ddenhart/ece411-practicum-2014/Project Model/ECE411_T10_LED_output_sequence_diagram.png

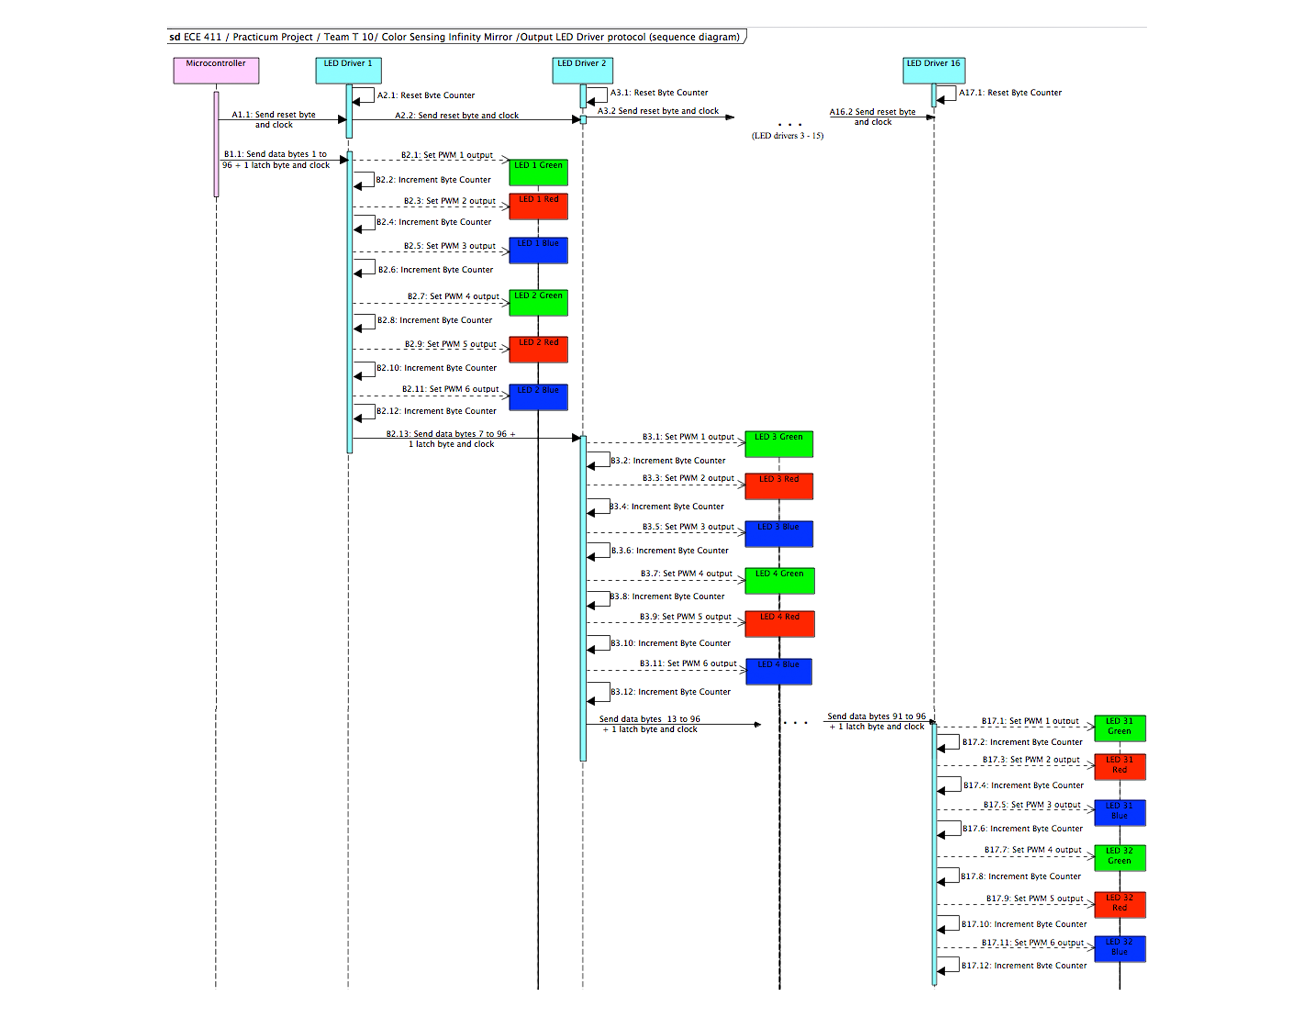
Project Model/ECE411_T10_LED_output_sequence_diagram.png
