ddenhart/ece411-practicum-2014/Project Model/T10-L0-AudioAmplifier.png

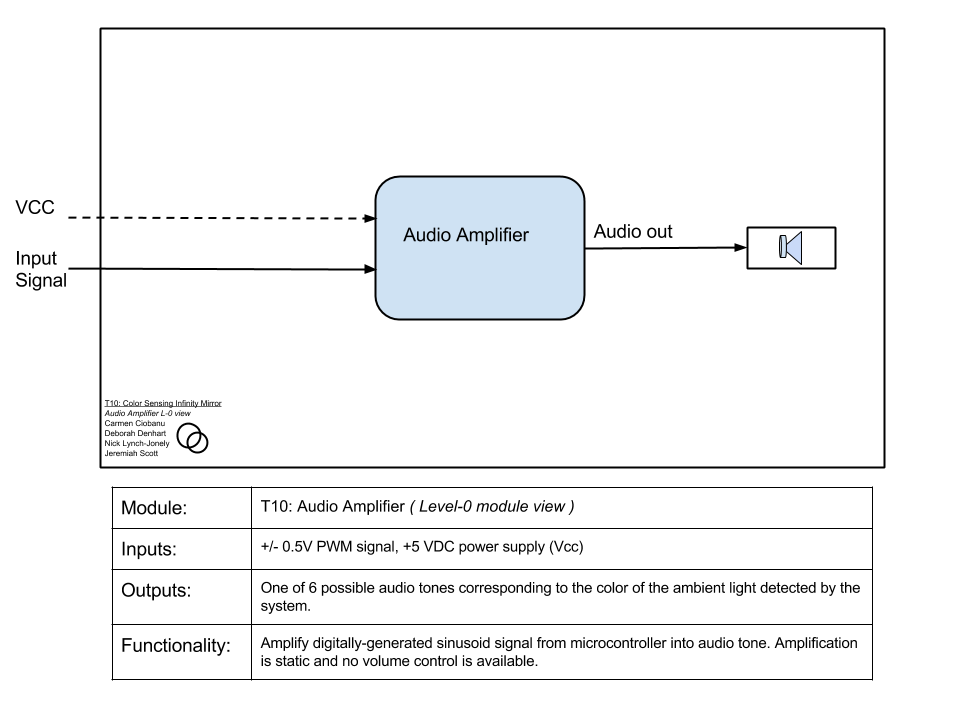
Project Model/T10-L0-AudioAmplifier.png
