ddenhart/ece411-practicum-2014/Project Model/T10-L0-blockdiagram_colorsensor.png

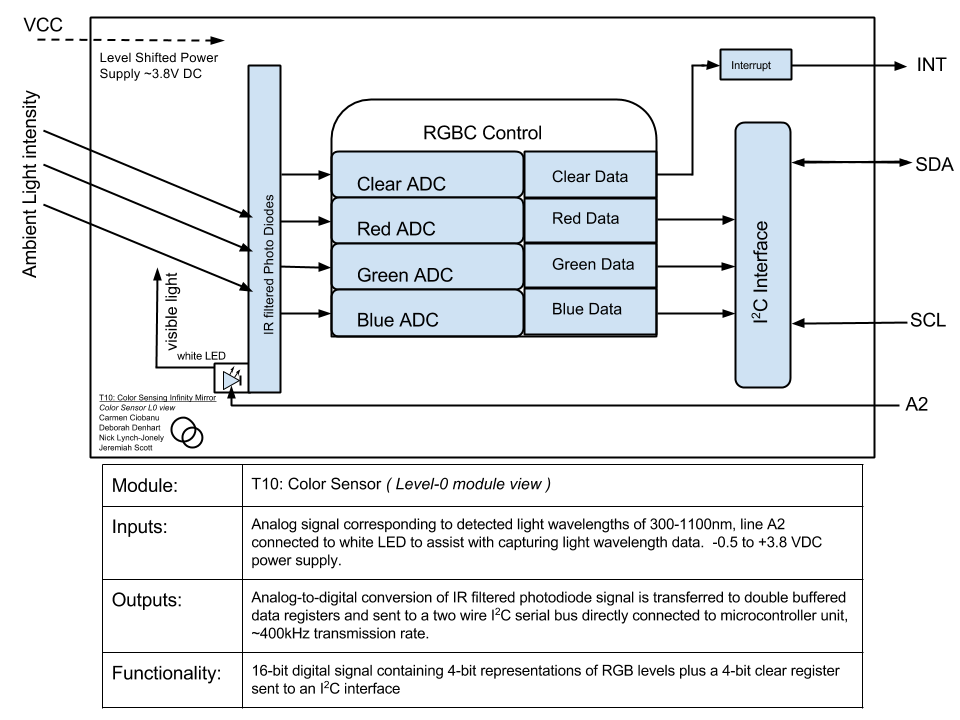
Project Model/T10-L0-blockdiagram_colorsensor.png
