ddenhart/ece411-practicum-2014/Project Model/T10-L0-blockdiagram_RGBLEDstrip.png

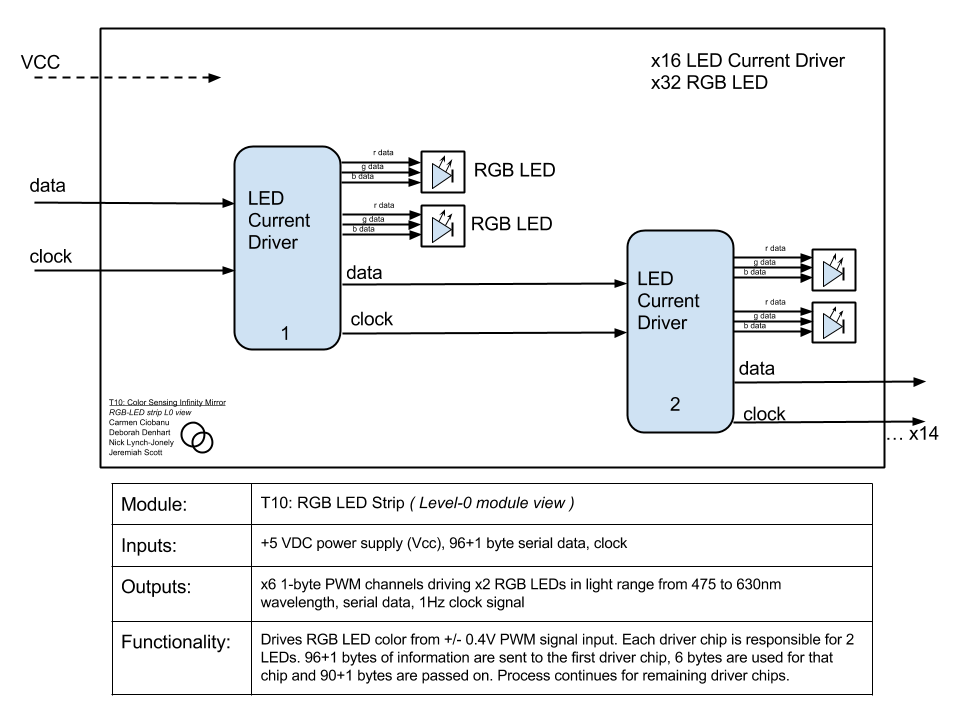
Project Model/T10-L0-blockdiagram_RGBLEDstrip.png
