ddenhart/ece411-practicum-2014/Project Model/T10-L1-blockdiagram_fullsystem.png

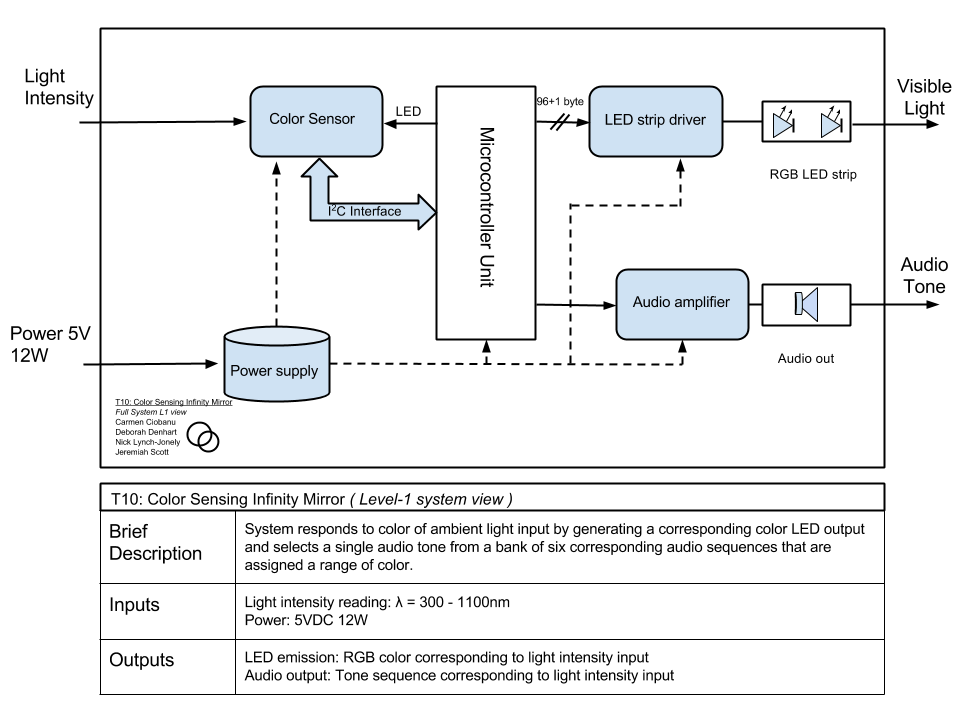
Project Model/T10-L1-blockdiagram_fullsystem.png
