ddenhart/ece411-practicum-2014/Project Model/T10_UML_activity_view_colorsensor.png

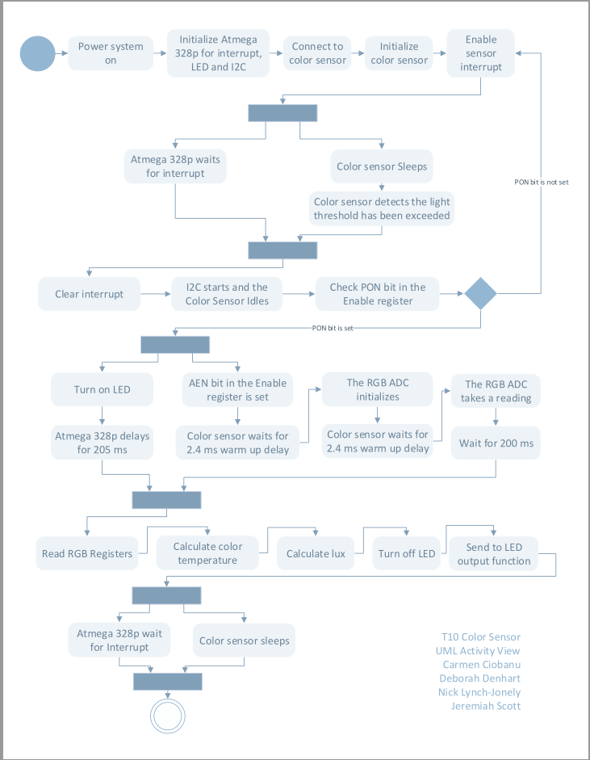
Project Model/T10_UML_activity_view_colorsensor.png
