ddenhart/ece411-practicum-2014/prototyping stage/colorSensorBlockDiagram.JPG

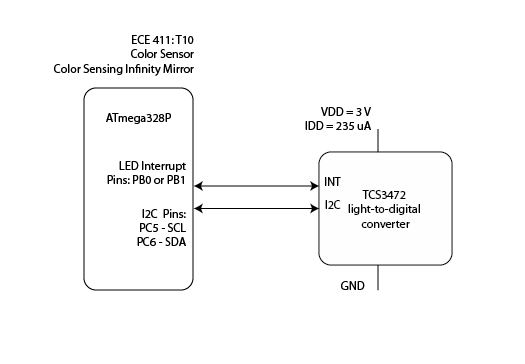
prototyping stage/colorSensorBlockDiagram.JPG
