ddenhart/ece411-practicum-2014/prototyping stage/T10_ECE411_LED_Output_Drawing.png

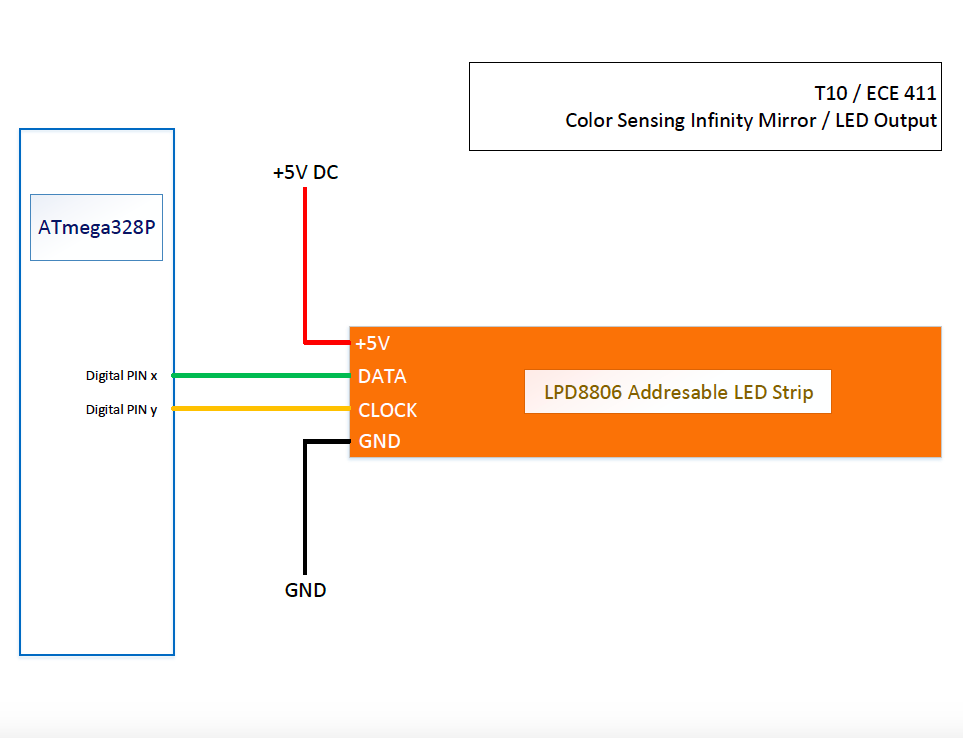
prototyping stage/T10_ECE411_LED_Output_Drawing.png
