ddenhart/ece411-practicum-2014/Schematic/board_layout_final2.png

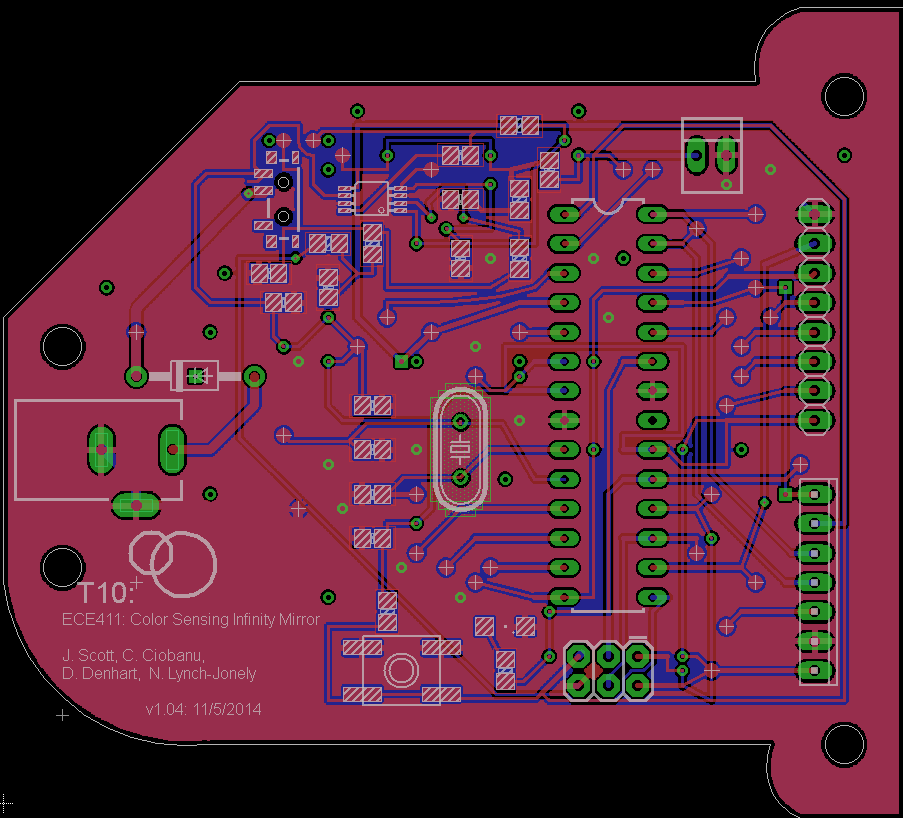
Schematic/board_layout_final2.png
