ddenhart/ece411-practicum-2014/Schematic/board_layout_final3.png

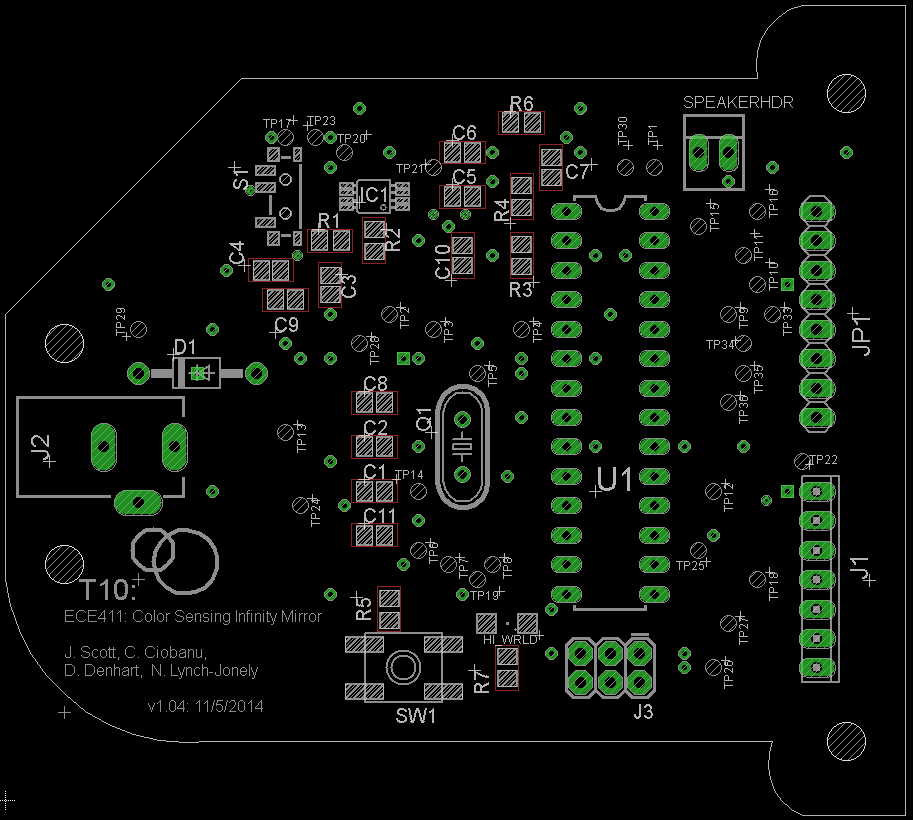
Schematic/board_layout_final3.png
