ddenhart/ece411-practicum-2014/Schematic/boardlayout_preliminary2.png

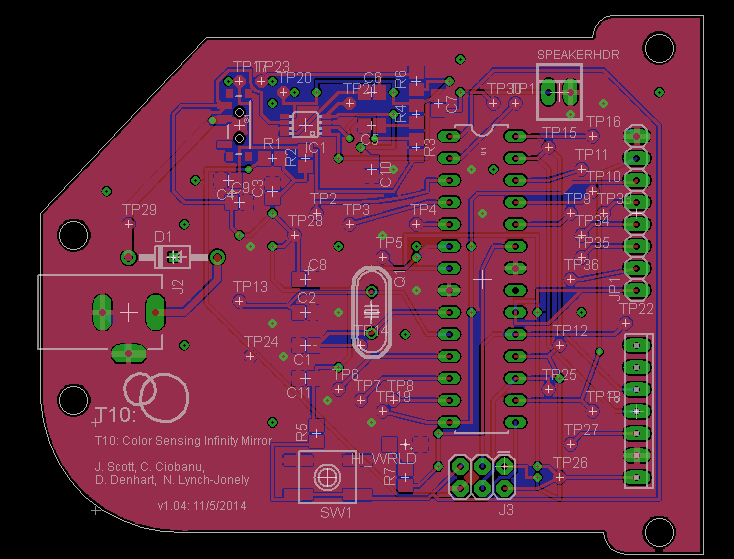
Schematic/boardlayout_preliminary2.png
