ddenhart/ece411-practicum-2014/Schematic/boardlayout_preliminary.png

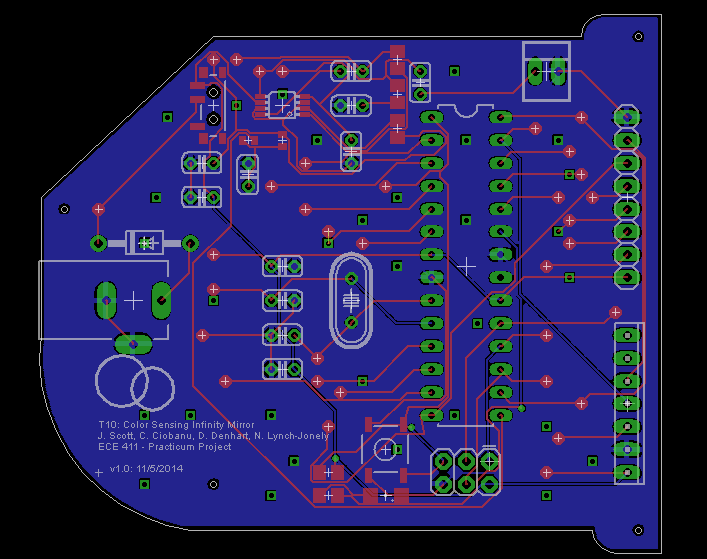
Schematic/boardlayout_preliminary.png
