ddenhart/ece411-practicum-2014/Schematic/oshpark renders/bottom.png

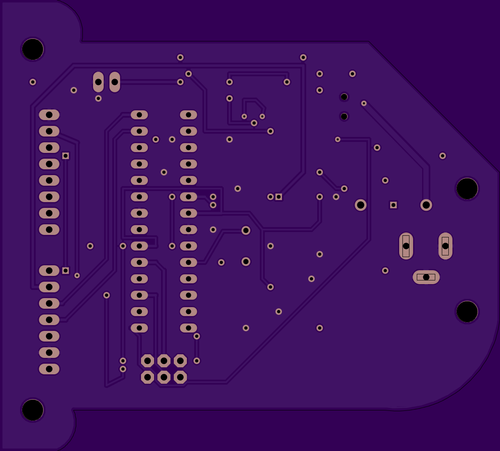
Schematic/oshpark renders/bottom.png
