ddenhart/ece411-practicum-2014/Schematic/oshpark renders/bottommask.png

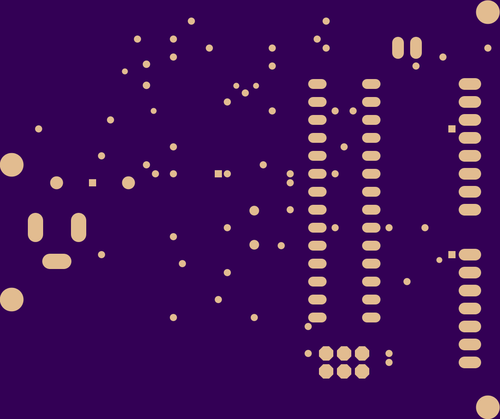
Schematic/oshpark renders/bottommask.png
