ddenhart/ece411-practicum-2014/Schematic/oshpark renders/dimension.png

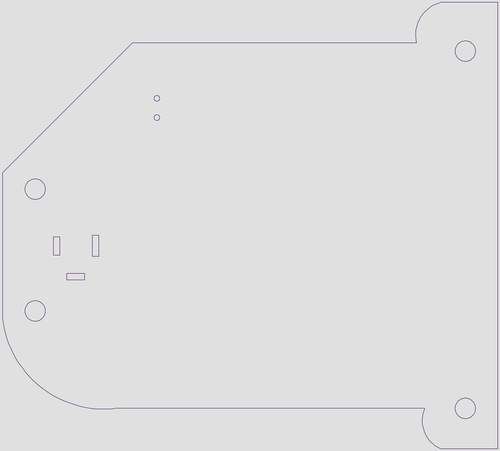
Schematic/oshpark renders/dimension.png
