ddenhart/ece411-practicum-2014/Schematic/oshpark renders/top.png

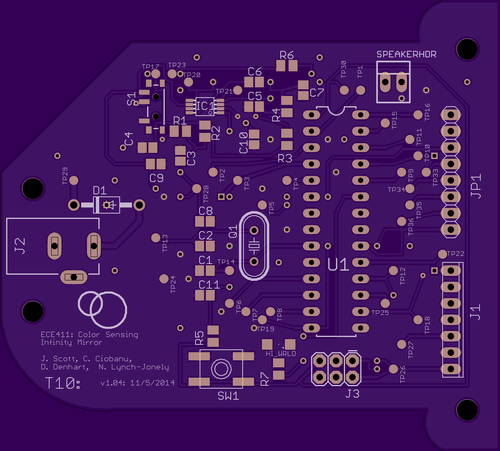
Schematic/oshpark renders/top.png
