ddenhart/ece411-practicum-2014/Schematic/oshpark renders/tSilk.png

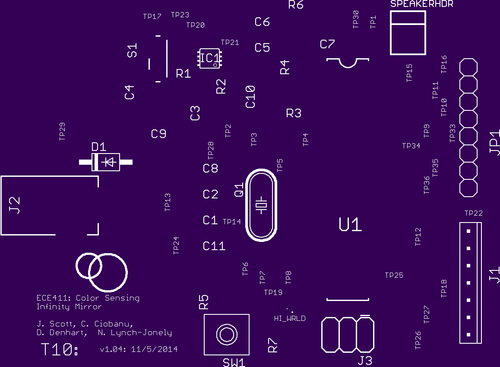
Schematic/oshpark renders/tSilk.png
