ddenhart/ece411-practicum-2014/Schematic/schematic_final.png

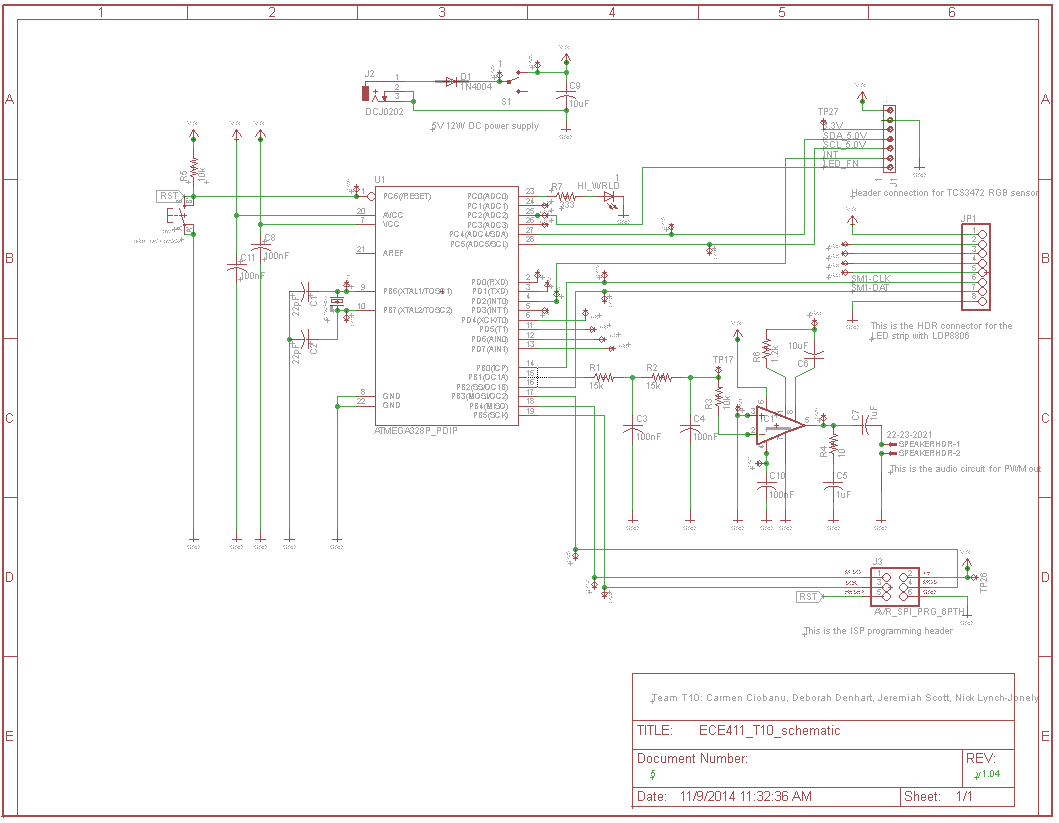
Schematic/schematic_final.png
