ddenhart/ece411-practicum-2014/Schematic/terribleroughdraft.png

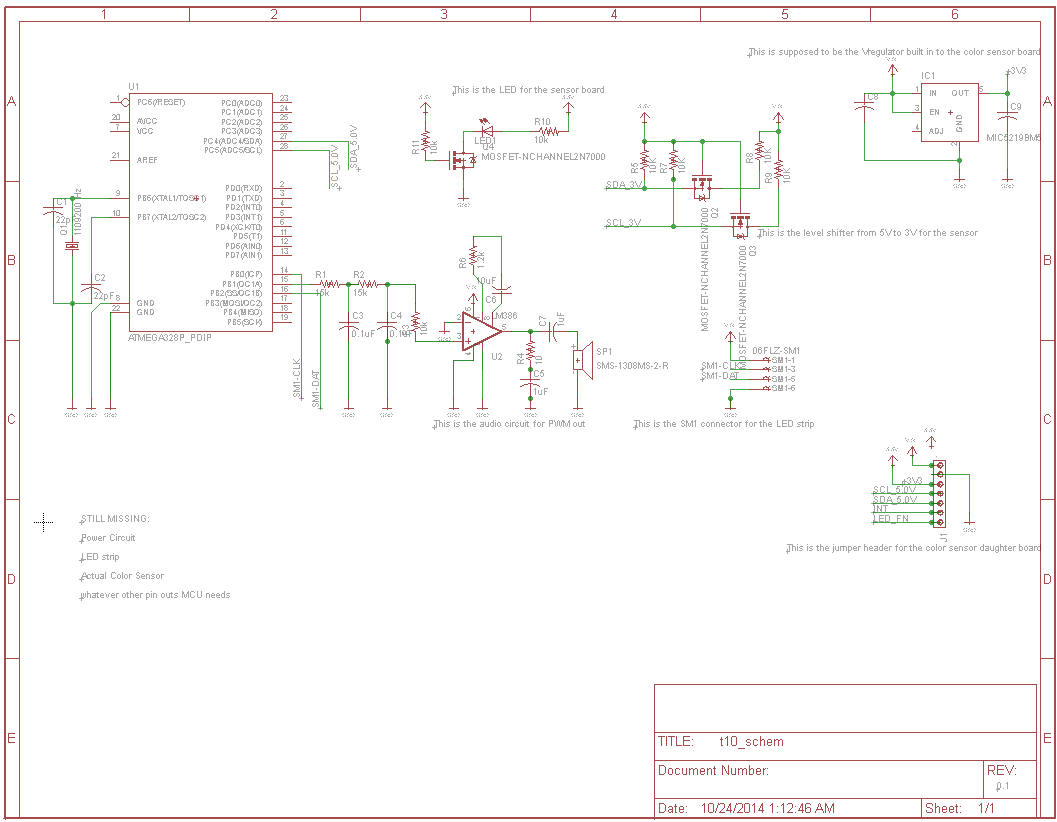
Schematic/terribleroughdraft.png
