ddenhart/ece411-practicum-2014/Schematic/DRC_results.png

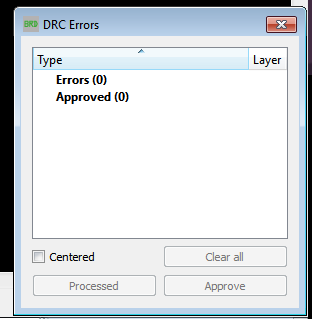
Schematic/DRC_results.png
