ddenhart/ece411-practicum-2014/Schematic/ERC results_preliminaryschematicv1_01.png

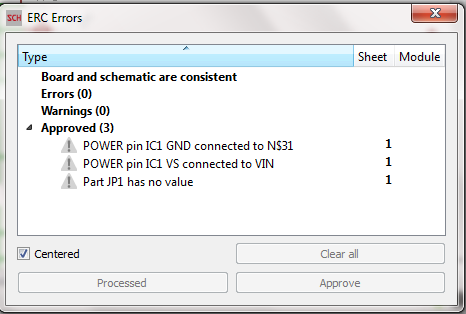
Schematic/ERC results_preliminaryschematicv1_01.png
